qwazwsx/Unix-Time-Clock/Firmware-ESP32/getTime.h

#ifndef gettime_h
#define gettime_h

#include "arduino.h"

#ifdef __cplusplus
extern "C" {
#endif

// for unix time:
void coreTask(void * pvParameters);
int isConnecting(void);
void getTimeFromInternet(void);
void startHardwareTimer(void) ;
unsigned int getTime(void);

#ifdef __cplusplus
}
#endif

#endif
